QuinnFreedman/modular/modules/Mixer/README.md

<div class="fm-readme-container">
<div class="fm-row">



<div class="fm-readme-text">

<h1>Mixer</h1>

<p>A 5-input active mixer for audio or CV. Can be daisy-chained together for larger mixes.</p>

<h2>Resources</h2>

<ul>
  <li><a href="https://quinnfreedman.github.io/fm-artifacts/Mixer/mixer_manual.pdf">Manual</a></li>
  <li><a href="https://quinnfreedman.github.io/modular/modules/Mixer/docs/assembly_instructions">Assembly instructions and BOM</a></li>
  <li><a href="https://quinnfreedman.github.io/fm-artifacts/Mixer/mixer_pcb_interactive_bom.html">Interactive BOM</a></li>
  <li><a href="https://quinnfreedman.github.io/fm-artifacts/Mixer/mixer_faceplate.svg">Faceplate stencil SVG</a></li>
  <li>GERBER files:
    <ul>
      <li>Faceplate: <a href="https://quinnfreedman.github.io/fm-artifacts/Mixer/mixer_faceplate_jlcpcb.zip">JLCPCB</a>, <a href="https://quinnfreedman.github.io/fm-artifacts/Mixer/mixer_faceplate_pcbway.zip">PCBway</a></li>
      <li>PCB: <a href="https://quinnfreedman.github.io/fm-artifacts/Mixer/mixer_jlcpcb.zip">JLCPCB</a>, <a href="https://quinnfreedman.github.io/fm-artifacts/Mixer/mixer_pcbway.zip">PCBway</a></li>
    </ul>
  </li>
  <li>Parts on Tayda <a href="https://www.taydaelectronics.com/savecartpro/index/savenewquote/qid/39240677892">cart link</a>, <a href="https://freemodular.org/modules/Mixer/fm_mixer_tayda_bom.csv">quick-order CSV</a></li>
  <li><a href="https://github.com/QuinnFreedman/modular/tree/main/modules/Mixer">Source files</a></li>
  <li><a href="https://quinnfreedman.github.io/fm-artifacts/Mixer/mixer_schematic.pdf">Schematic PDF</a></li>
</ul>

</div>
</div>

<h2>Details</h2>

<b>DIY difficulty:</b> Very easy<br>
<b>HP:</b> 8<br>
<b>Power usage:</b>
<table class="fm-current-table">
  <tr>
    <th></th>
    <th>Typical</th>
    <th>Maximum</th>
  </tr>
  <tr>
    <td>+5V</td>
    <td>NC</td>
    <td>-</td>
  </tr>
  <tr>
    <td>+12V</td>
    <td>4mA</td>
    <td>5mA</td>
  </tr>
  <tr>
    <td>-12V</td>
    <td>4mA</td>
    <td>5mA</td>
  </tr>
</table>

<a class="fm-etsy-link" href="https://www.etsy.com/listing/1804937947">
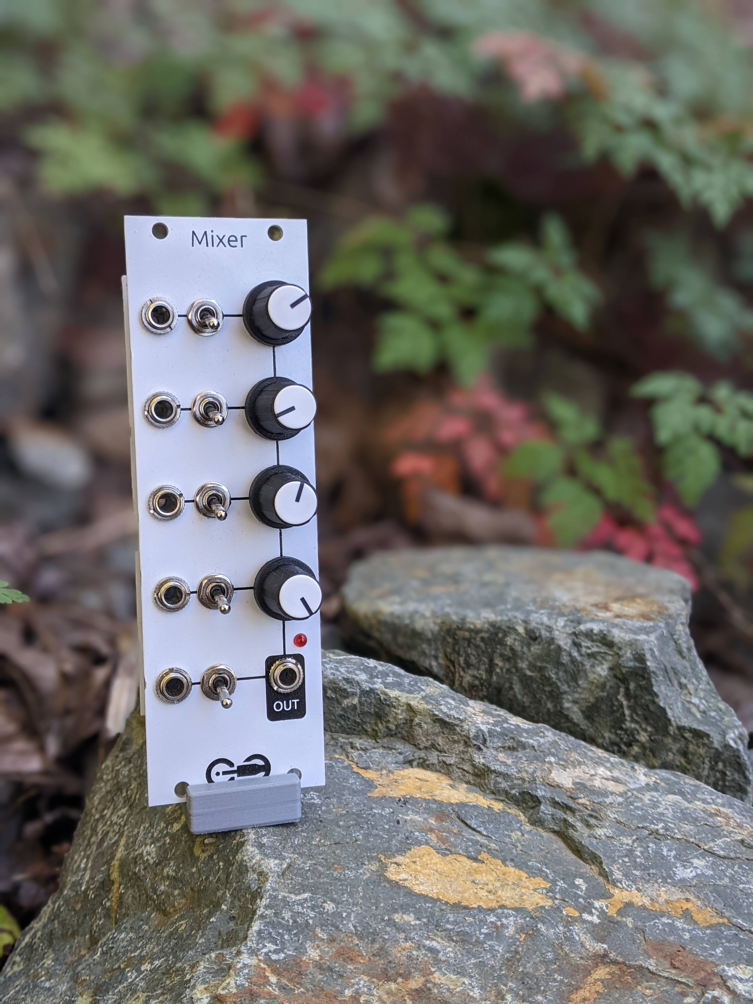
[picture p18: modules/Mixer/docs/images/00-mixer-front.jpg]
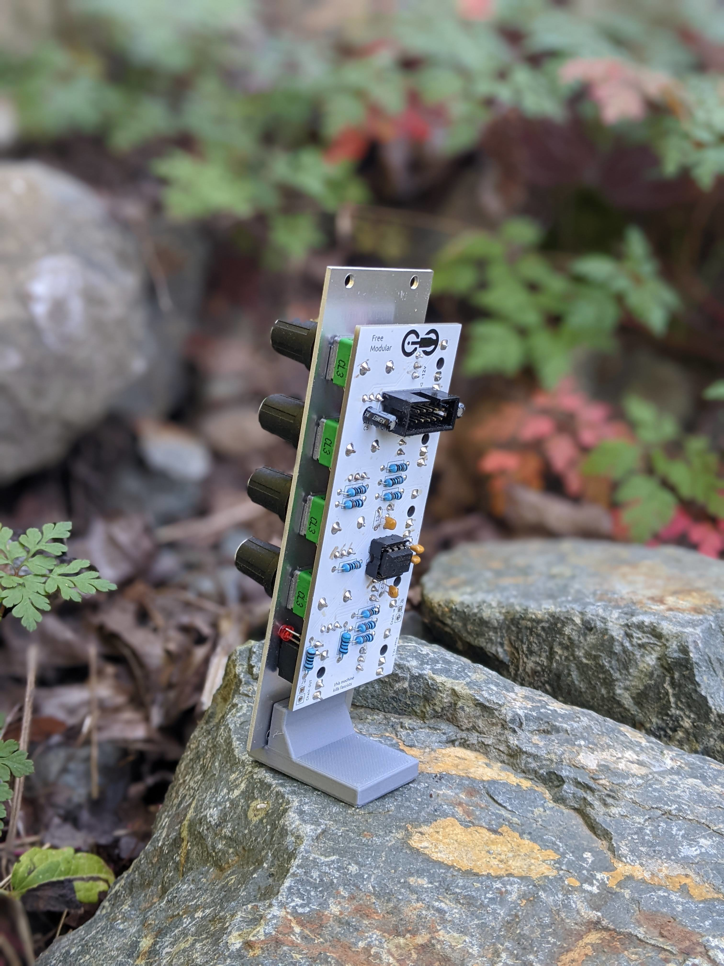
[picture p19: modules/Mixer/docs/images/01-mixer-back.jpg]
  
  <h3>Available on Etsy</h3>
  <p>You can buy PCBs, full kits, or hand-assembled modules directly from me on Etsy</p>
</a>

</div>
