QuinnFreedman/modular/modules/OffsetAtten/README.md

<div class="fm-readme-container">
<div class="fm-row">



<div class="fm-readme-text">

<h1>Offset/Atten</h1>

<p>A utility module to scale, shift, and invert signals. Has two identical, independent channels. Each can attenuvert (attenuate and/or invert) an input voltage and add a constant offset voltage.</p>

<h2>Resources</h2>

<ul>
  <li><a href="https://quinnfreedman.github.io/fm-artifacts/OffsetAtten/offset_atten_manual.pdf">Manual</a></li>
  <li><a href="https://quinnfreedman.github.io/modular/modules/OffsetAtten/docs/assembly_instructions">Assembly instructions and BOM</a></li>
  <li>Interactive BOM: <a href="https://quinnfreedman.github.io/fm-artifacts/OffsetAtten/offset_atten_pcb_front_interactive_bom.html">front panel</a>, <a href="https://quinnfreedman.github.io/fm-artifacts/OffsetAtten/offset_atten_pcb_back_interactive_bom.html">back panel</a></li>
  <li><a href="https://quinnfreedman.github.io/fm-artifacts/OffsetAtten/offset_atten_faceplate.svg">Faceplate stencil SVG</a></li>
  <li>GERBER files:
    <ul>
      <li>Faceplate: <a href="https://quinnfreedman.github.io/fm-artifacts/OffsetAtten/offset_atten_faceplate_jlcpcb.zip">JLCPCB</a>, <a href="https://quinnfreedman.github.io/fm-artifacts/OffsetAtten/offset_atten_faceplate_pcbway.zip">PCBway</a></li>
      <li>Front panel: <a href="https://quinnfreedman.github.io/fm-artifacts/OffsetAtten/offset_atten_pcb_front_jlcpcb.zip">JLCPCB</a>, <a href="https://quinnfreedman.github.io/fm-artifacts/OffsetAtten/offset_atten_pcb_front_pcbway.zip">PCBway</a></li>
      <li>Back panel: <a href="https://quinnfreedman.github.io/fm-artifacts/OffsetAtten/offset_atten_pcb_back_jlcpcb.zip">JLCPCB</a>, <a href="https://quinnfreedman.github.io/fm-artifacts/OffsetAtten/offset_atten_pcb_back_pcbway.zip">PCBway</a></li>
    </ul>
  </li>
  <li>Parts on Tayda: <a href="https://www.taydaelectronics.com/savecartpro/index/savenewquote/qid/87940674120">cart link</a>, <a href="https://freemodular.org/modules/OffsetAtten/fm_oa_tayda_bom.csv">quick-order CSV</a></li>
  <li><a href="https://github.com/QuinnFreedman/modular/tree/main/modules/OffsetAtten">Source files</a></li>
  <li><a href="https://quinnfreedman.github.io/fm-artifacts/OffsetAtten/offset_atten_schematic.pdf">Schematic PDF</a></li>
</ul>

</div>
</div>

<h2>Details</h2>

<b>DIY difficulty:</b> Very easy<br>
<b>HP:</b> 4<br>
<b>Power usage:</b>
<table class="fm-current-table">
  <tr>
    <th></th>
    <th>Typical</th>
    <th>Maximum with typical connections</th>
    <th>Absolute maximum (all outputs shorted to ground)</th>
  </tr>
  <tr>
    <td>+5V</td>
    <td>NC</td>
    <td>-</td>
    <td>-</td>
  </tr>
  <tr>
    <td>+12V</td>
    <td>17mA</td>
    <td>25mA</td>
    <td>41mA</td>
  </tr>
  <tr>
    <td>-12V</td>
    <td>17mA</td>
    <td>24mA</td>
    <td>37mA</td>
  </tr>
</table>

<a class="fm-etsy-link" href="https://www.etsy.com/listing/1788670334">
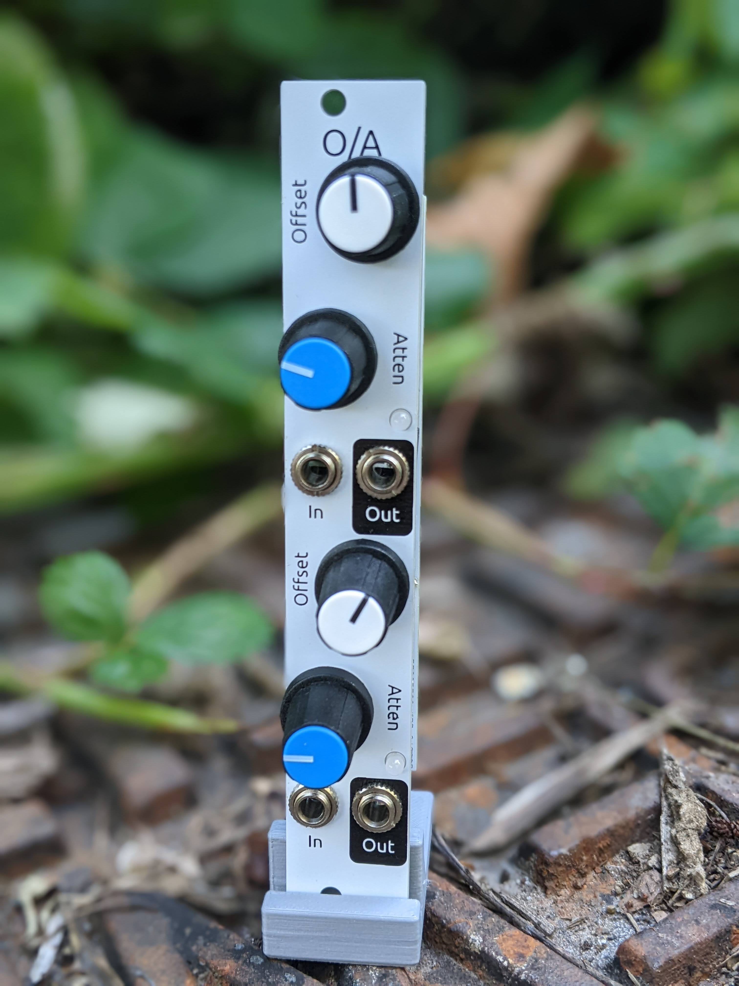
[picture p20: modules/OffsetAtten/docs/images/00-offsetatten-front.jpg]
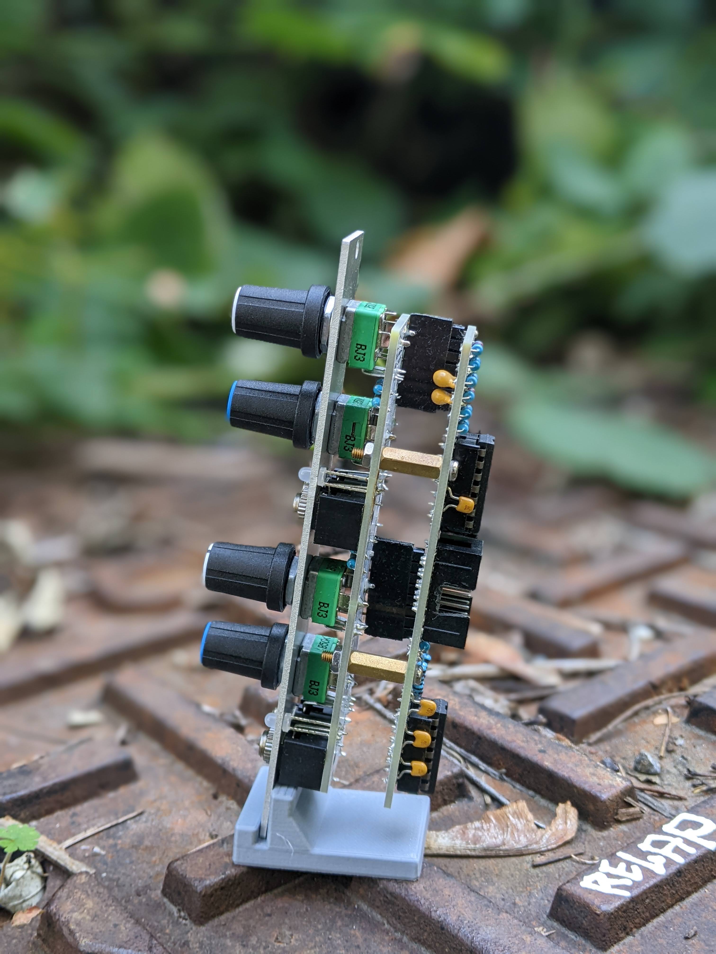
[picture p21: modules/OffsetAtten/docs/images/01-offsetatten-back.jpg]
  
  <h3>Available on Etsy</h3>
  <p>You can buy PCBs, full kits, or hand-assembled modules directly from me on Etsy</p>
</a>

</div>
