QuinnFreedman/modular/modules/Output/README.md

<div class="fm-readme-container">
<div class="fm-row">



<div class="fm-readme-text">

<h1>Output</h1>

<p>A stereo line out and headphone amp with VU meter</p>

<h2>Resources</h2>

<ul>
  <li><a href="https://quinnfreedman.github.io/fm-artifacts/Output/output_manual.pdf">Manual</a></li>
  <li><a href="https://quinnfreedman.github.io/modular/modules/Output/docs/assembly_instructions">Assembly instructions and BOM</a></li>
  <li>Interactive BOM: <a href="https://quinnfreedman.github.io/fm-artifacts/Output/output_pcb_front_interactive_bom.html">front panel</a>, <a href="https://quinnfreedman.github.io/fm-artifacts/Output/output_pcb_middle_interactive_bom.html">middle panel</a>, <a href="https://quinnfreedman.github.io/fm-artifacts/Output/output_pcb_back_interactive_bom.html">back panel</a></li>
  <li><a href="https://quinnfreedman.github.io/fm-artifacts/Output/output_faceplate.svg">Faceplate stencil SVG</a></li>
  <li>GERBER files:
    <ul>
      <li>Faceplate: <a href="https://quinnfreedman.github.io/fm-artifacts/Output/output_faceplate_jlcpcb.zip">JLCPCB</a>, <a href="https://quinnfreedman.github.io/fm-artifacts/Output/output_faceplate_pcbway.zip">PCBway</a></li>
      <li>Front panel: <a href="https://quinnfreedman.github.io/fm-artifacts/Output/output_pcb_front_jlcpcb.zip">JLCPCB</a>, <a href="https://quinnfreedman.github.io/fm-artifacts/Output/output_pcb_front_pcbway.zip">PCBway</a></li>
      <li>Middle panel: <a href="https://quinnfreedman.github.io/fm-artifacts/Output/output_pcb_middle_jlcpcb.zip">JLCPCB</a>, <a href="https://quinnfreedman.github.io/fm-artifacts/Output/output_pcb_middle_pcbway.zip">PCBway</a></li>
      <li>Back panel: <a href="https://quinnfreedman.github.io/fm-artifacts/Output/output_pcb_back_jlcpcb.zip">JLCPCB</a>, <a href="https://quinnfreedman.github.io/fm-artifacts/Output/output_pcb_back_pcbway.zip">PCBway</a></li>
    </ul>
  </li>
  <li>(Most) parts on Tayda: <a href="https://www.taydaelectronics.com/savecartpro/index/savenewquote/qid/50242216928">cart link</a>, <a href="https://freemodular.org/modules/Output/fm_output_tayda_bom.csv">quick-order CSV</a></li>
  <li><a href="https://github.com/QuinnFreedman/modular/tree/main/modules/Output">Source files</a></li>
  <li><a href="https://quinnfreedman.github.io/fm-artifacts/Output/output_schematic.pdf">Schematic</a></li>
</ul>

</div>
</div>

<h2>Details</h2>

<b>DIY difficulty:</b> Medium (nothing crazy but there are a lot of parts)<br>
<b>HP:</b> 8<br>
<b>Power usage:</b>
<table class="fm-current-table">
  <tr>
    <th></th>
    <th>Current draw</th>
  </tr>
  <tr>
    <td>+5V</td>
    <td>-</td>
  </tr>
  <tr>
    <td>+12V</td>
    <td>100mA</td>
  </tr>
  <tr>
    <td>-12V</td>
    <td>95mA</td>
  </tr>
</table>

<a class="fm-etsy-link" href="https://www.etsy.com/listing/1804957539">
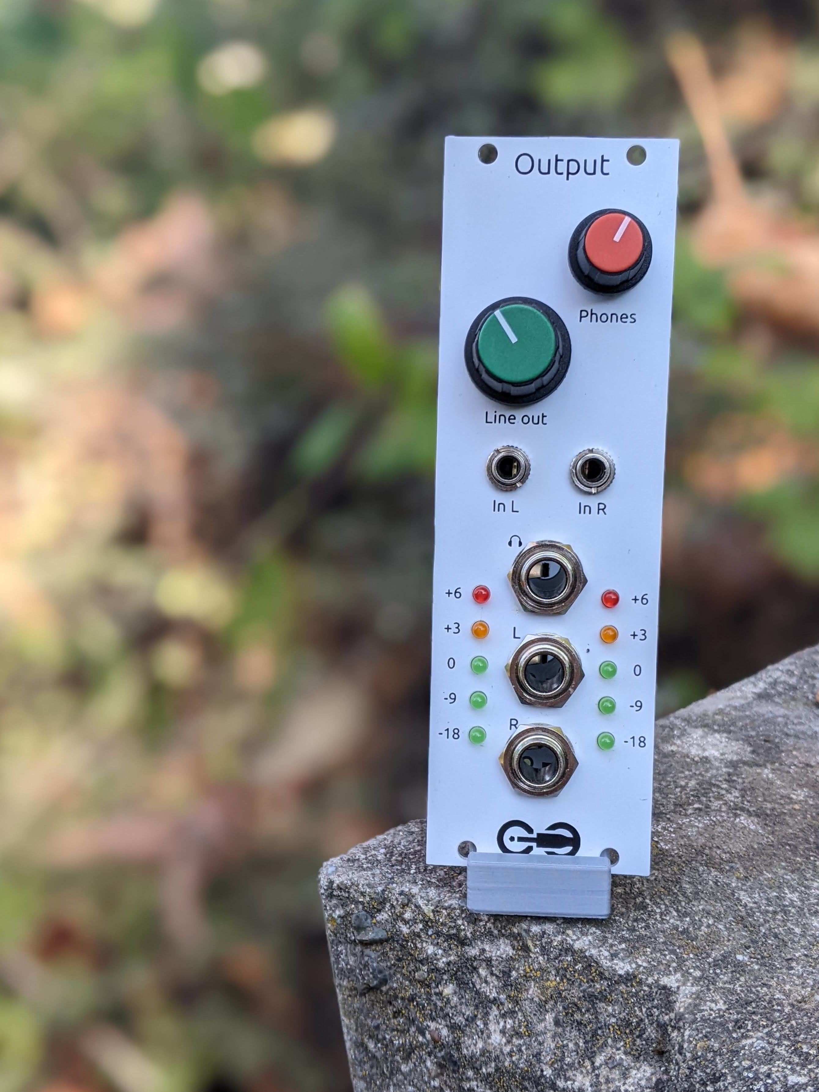
[picture p22: modules/Output/docs/images/00-output-front.jpg]
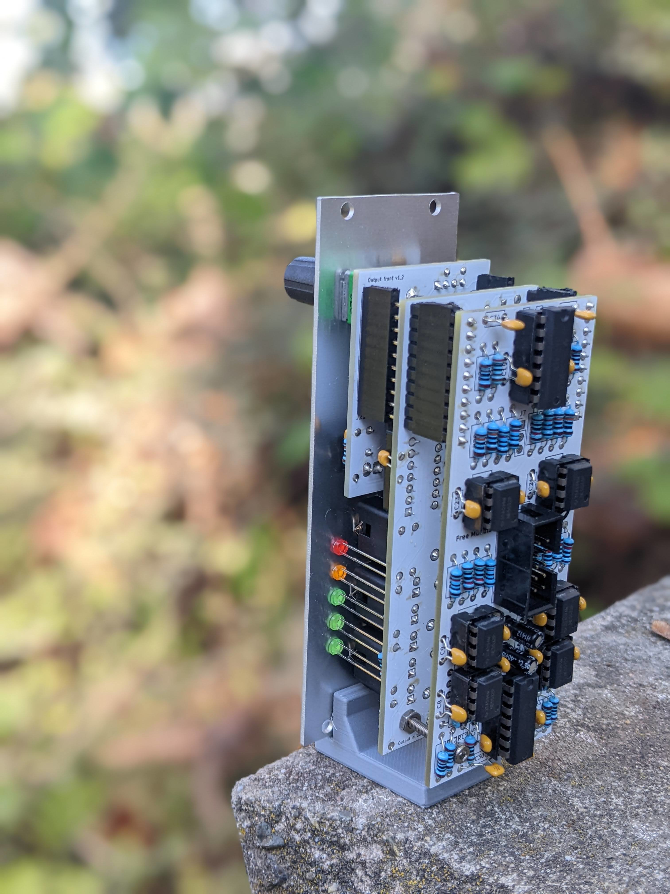
[picture p23: modules/Output/docs/images/01-output-back.jpg]
  
  <h3>Available on Etsy</h3>
  <p>You can buy PCBs, full kits, or hand-assembled modules directly from me on Etsy</p>
</a>

</div>
