QuinnFreedman/modular/modules/devboard/README.md

# Development Board

This is not a module meant for production. This is a development board I use for prototyping modules on breadboard. It's just in this repo so that I can build it with the same build script. Feel free to use it if you want, though.
