QuinnFreedman/modular/docs/images/avrdudess_screenshot.png

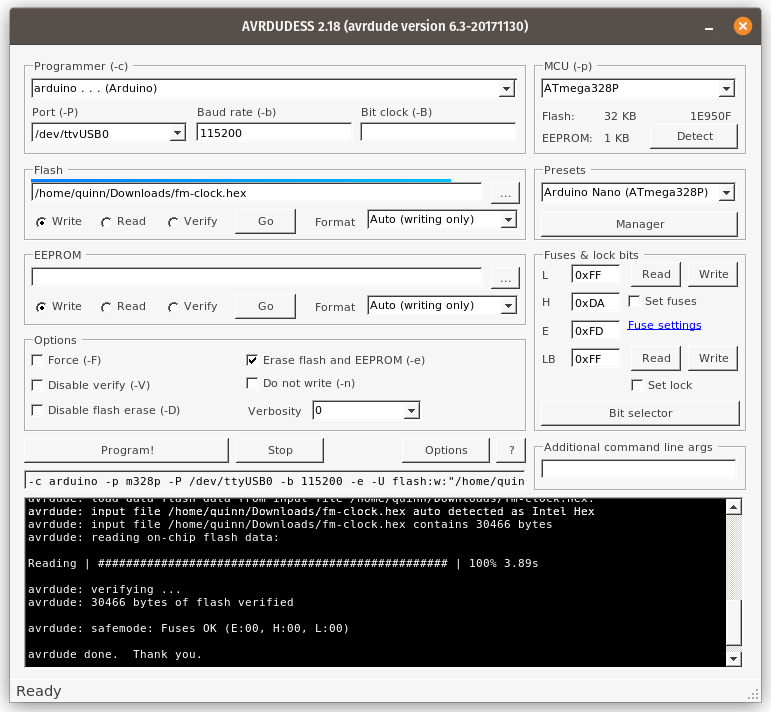
docs/images/avrdudess_screenshot.png
